sensorable/g935-enclosure/img/houston-radar-ss400-front.jpg

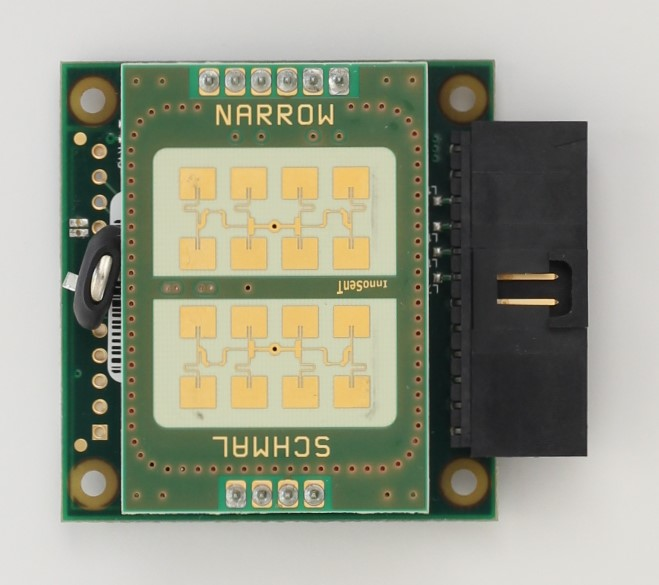
img/houston-radar-ss400-front.jpg
